dijkstrw/5x5x2/schematic/docs/MUP_U22401/1593657581940577.jpg

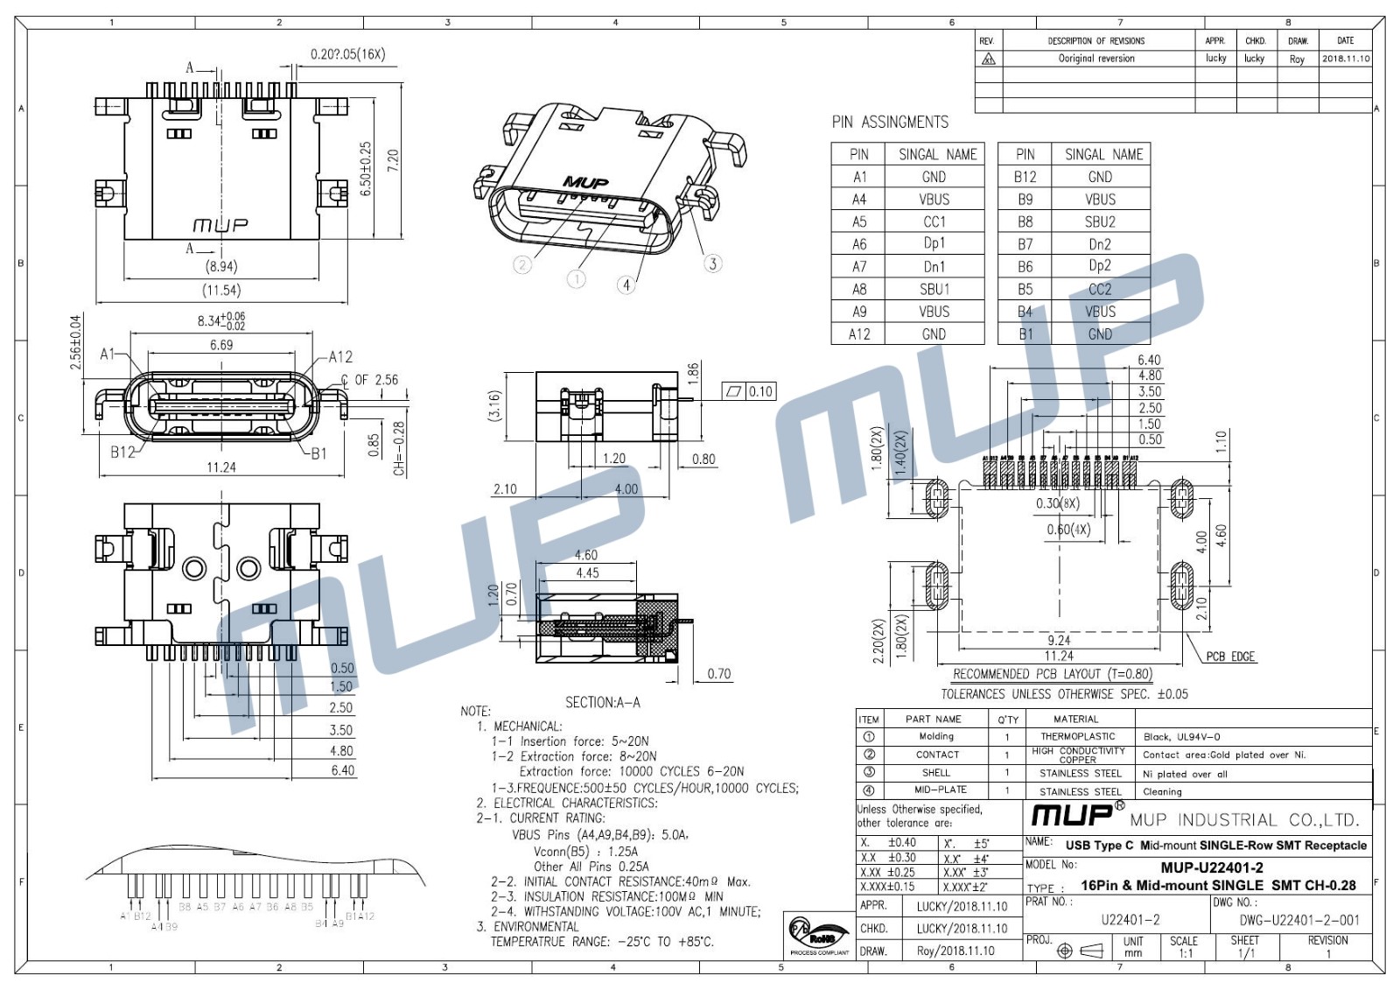
schematic/docs/MUP_U22401/1593657581940577.jpg
