dijkstrw/5x5x2/schematic/docs/MUP_U22401/1593657582415781.jpg

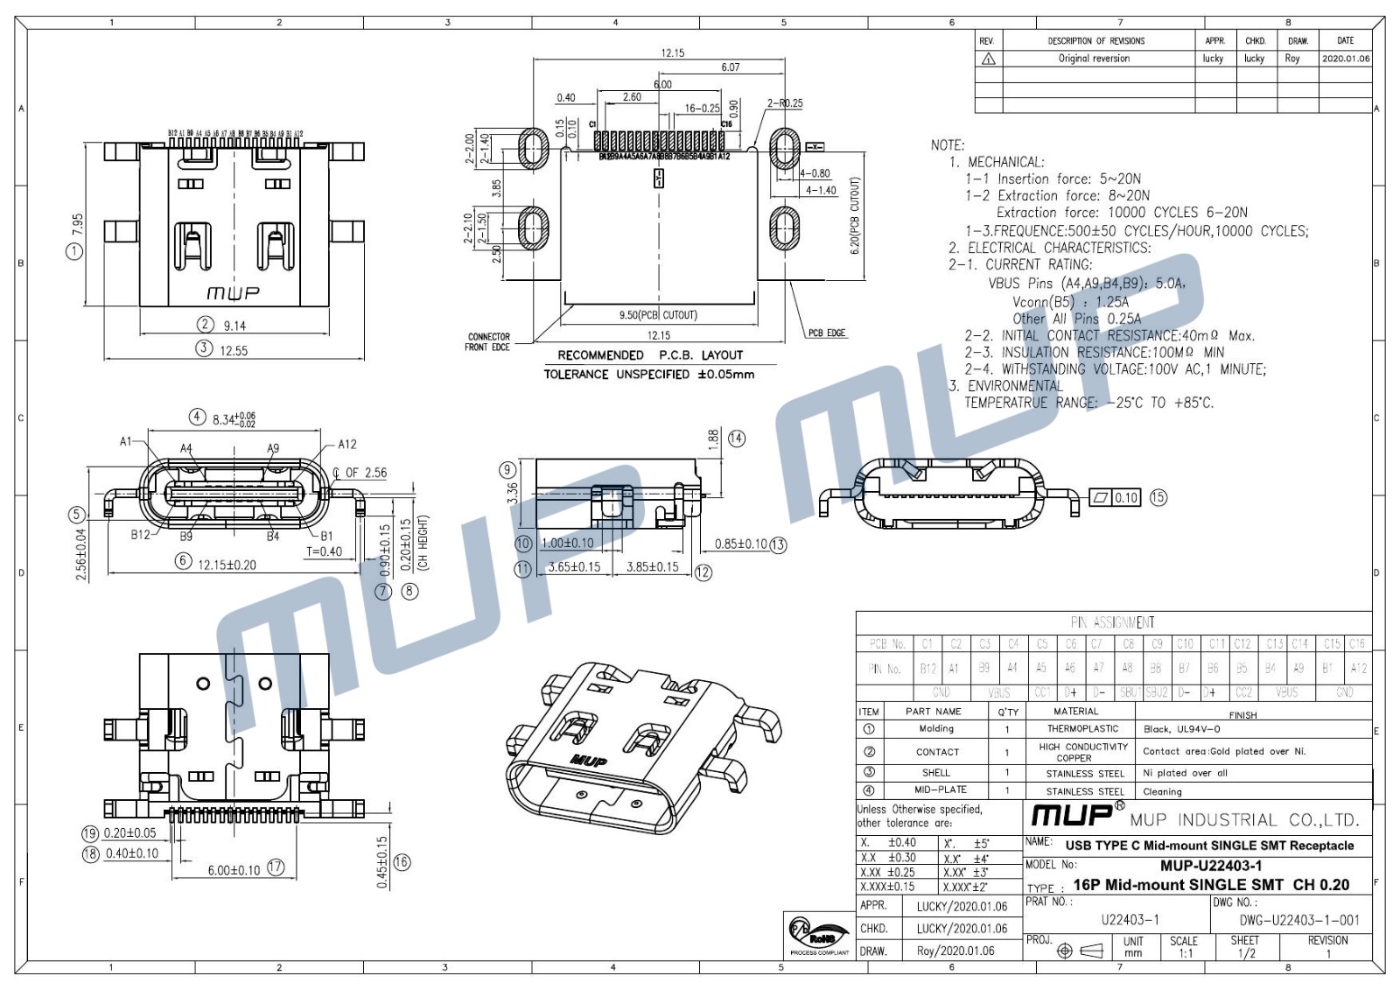
schematic/docs/MUP_U22401/1593657582415781.jpg
