dijkstrw/5x5x2/schematic/docs/MUP_U22401/1593657582979578.jpg

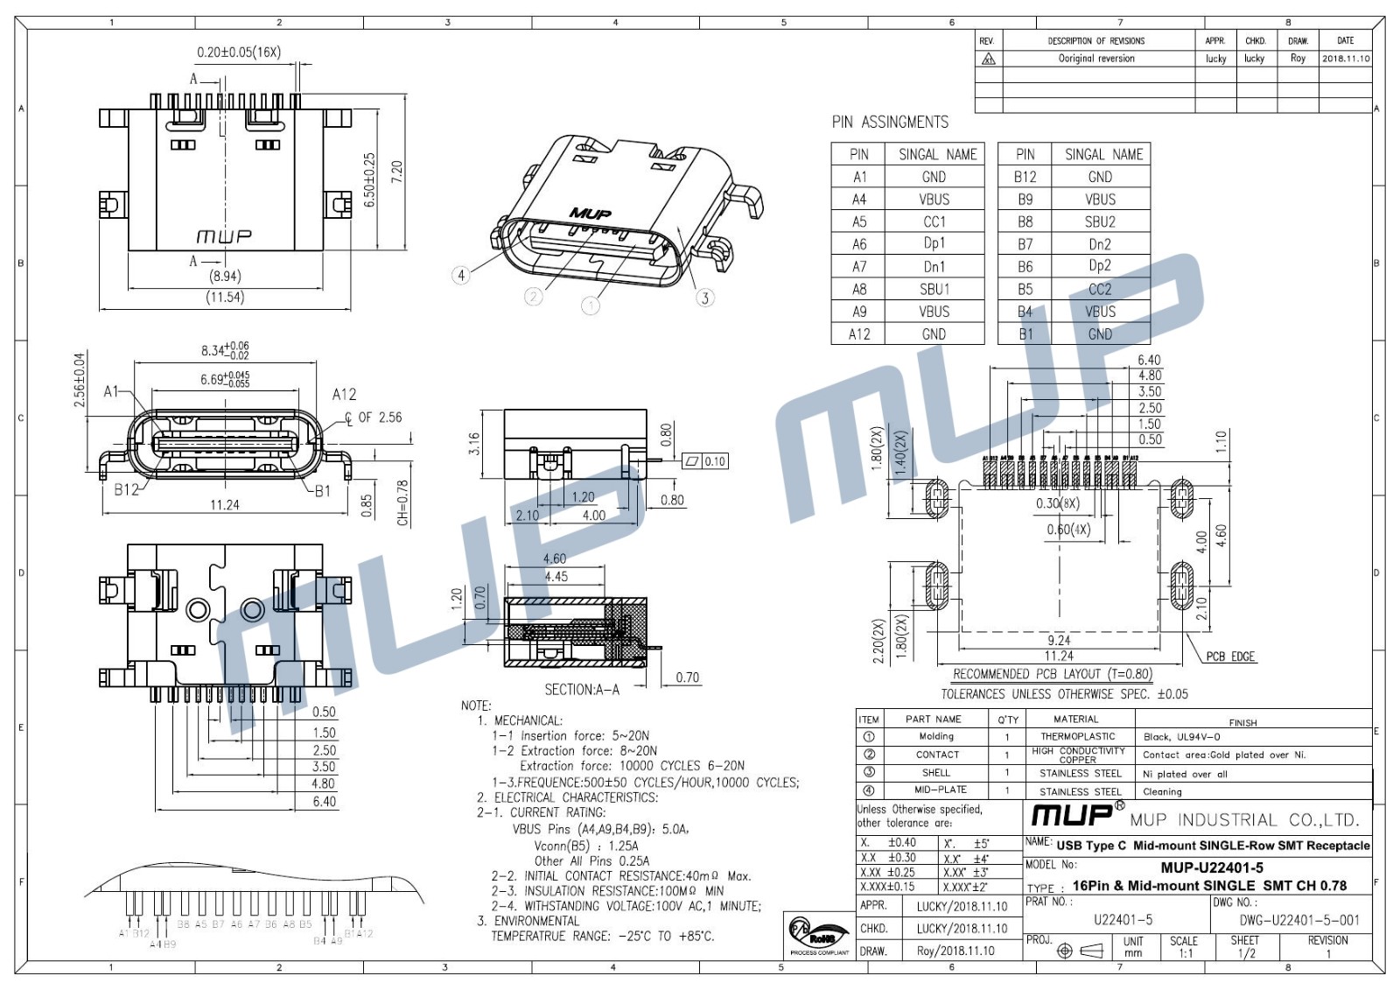
schematic/docs/MUP_U22401/1593657582979578.jpg
