dijkstrw/5x5x2/enclosure/third_plate.scad

include <dimension.scad>;
include <plate.scad>;

if (PROJECTION) {
  projection()
    third_plate();
 } else {
  third_plate();
 }
