dijkstrw/5x5x2/enclosure/top_plate.scad

include <plate.scad>;

if (PROJECTION) {
  projection(cut=true)
    top_plate();
 } else {
  top_plate();
 }
