dijkstrw/5x5x2/light.c

/*
 * Copyright (c) 2023 by Willem Dijkstra <wpd@xs4all.nl>.
 * All rights reserved.
 *
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
 * THIS SOFTWARE IS PROVIDED BY THE COPYRIGHT HOLDERS AND CONTRIBUTORS "AS IS"
 * AND ANY EXPRESS OR IMPLIED WARRANTIES, INCLUDING, BUT NOT LIMITED TO, THE
 * IMPLIED WARRANTIES OF MERCHANTABILITY AND FITNESS FOR A PARTICULAR PURPOSE
 * ARE DISCLAIMED. IN NO EVENT SHALL THE AUTHOR BE LIABLE FOR ANY DIRECT,
 * INDIRECT, INCIDENTAL, SPECIAL, EXEMPLARY, OR CONSEQUENTIAL DAMAGES
 * (INCLUDING, BUT NOT LIMITED TO, PROCUREMENT OF SUBSTITUTE GOODS OR SERVICES;
 * LOSS OF USE, DATA, OR PROFITS; OR BUSINESS INTERRUPTION) HOWEVER CAUSED AND
 * ON ANY THEORY OF LIABILITY, WHETHER IN CONTRACT, STRICT LIABILITY, OR TORT
 * (INCLUDING NEGLIGENCE OR OTHERWISE) ARISING IN ANY WAY OUT OF THE USE OF THIS
 * SOFTWARE, EVEN IF ADVISED OF THE POSSIBILITY OF SUCH DAMAGE.
 */

#include <stdint.h>
#include <string.h>

#include "config.h"
#include "elog.h"
#include "layer.h"
#include "light.h"
#include "macro.h"
#include "palette.h"
#include "rgbease.h"
#include "rgbmap.h"

lightmap_t lightmap =
{
    .data[0] = {
        { LIGHT_DESKTOP, LIGHT_DESKTOP, LIGHT_DESKTOP, LIGHT_DESKTOP, LIGHT_MUTE       },
        { LIGHT_DESKTOP, LIGHT_DESKTOP, LIGHT_DESKTOP, LIGHT_DESKTOP, LIGHT_DESKTOP    },
        { LIGHT_VOLUME,  LIGHT_VOLUME,  LIGHT_VOLUME,  LIGHT_VOLUME,  LIGHT_VOLUME     },
        { LIGHT_MACRO,   LIGHT_MACRO,   LIGHT_MACRO,   LIGHT_MACRO,   LIGHT_MACRO      },
        { LIGHT_LAYER,   LIGHT_LAYER,   LIGHT_DESKTOP, LIGHT_DESKTOP, LIGHT_BACKLIGHT  },
    },
    {
        { LIGHT_DESKTOP, LIGHT_DESKTOP, LIGHT_DESKTOP, LIGHT_DESKTOP, LIGHT_MUTE       },
        { LIGHT_DESKTOP, LIGHT_DESKTOP, LIGHT_DESKTOP, LIGHT_DESKTOP, LIGHT_DESKTOP    },
        { LIGHT_VOLUME,  LIGHT_VOLUME,  LIGHT_VOLUME,  LIGHT_VOLUME,  LIGHT_VOLUME     },
        { LIGHT_MACRO,   LIGHT_MACRO,   LIGHT_MACRO,   LIGHT_MACRO,   LIGHT_MACRO      },
        { LIGHT_LAYER,   LIGHT_LAYER,   LIGHT_DESKTOP, LIGHT_DESKTOP, LIGHT_BACKLIGHT  },
    },
    {
        { LIGHT_DESKTOP, LIGHT_DESKTOP, LIGHT_DESKTOP, LIGHT_DESKTOP, LIGHT_MUTE       },
        { LIGHT_DESKTOP, LIGHT_DESKTOP, LIGHT_DESKTOP, LIGHT_DESKTOP, LIGHT_DESKTOP    },
        { LIGHT_VOLUME,  LIGHT_VOLUME,  LIGHT_VOLUME,  LIGHT_VOLUME,  LIGHT_VOLUME     },
        { LIGHT_MACRO,   LIGHT_MACRO,   LIGHT_MACRO,   LIGHT_MACRO,   LIGHT_MACRO      },
        { LIGHT_LAYER,   LIGHT_LAYER,   LIGHT_DESKTOP, LIGHT_DESKTOP, LIGHT_BACKLIGHT  },
    },
};

lightstate_t light_state;

void
light_dump()
{
    uint8_t l, r, c;

    for (l = 0; l < LAYERS_NUM; l++) {
        printfnl("layer %02x", l);
        for (r = 0; r < ROWS_NUM; r++) {
            printf("row %02x: ", r);
            for (c = 0; c < COLS_NUM; c++) {
                printf("%c ", lightmap.data[l][r][c]);
            }
            printf("\n\r");
        }
    }
}

void
light_init()
{
    memset(&light_state, 0, sizeof(light_state));
}

void
light_set(uint8_t l, uint8_t r, uint8_t c, uint8_t v)
{
    if ((l >= LAYERS_NUM) ||
        (r >= ROWS_NUM) ||
        (c >= COLS_NUM)) {
        elog("light position out of bounds");
        return;
    }

    if ((v == LIGHT_BACKLIGHT) ||
        (v == LIGHT_DESKTOP) ||
        (v == LIGHT_LAYER) ||
        (v == LIGHT_MACRO) ||
        (v == LIGHT_MUTE) ||
        (v == LIGHT_VOLUME)) {
        lightmap.data[l][r][c] = v;
    } else {
        elog("light type unknown");
    }
}

void
light_set_desktop(uint8_t ascreen, uint8_t adisplay)
{
    uint8_t s = ascreen % SCREENS_NUM;

    if (ascreen == 0) {
        for (s = 0; s < SCREENS_NUM; s++) {
            light_state.desktop[s] = adisplay;
        }
    } else {
        light_state.desktop[s - 1] = adisplay;
        if (s > light_state.max_screen) {
            light_state.max_screen = s;
        }
    }
    light_apply_state(LIGHT_DESKTOP);
}

void
light_set_layer(uint8_t alayer)
{
    light_apply_state(0);
}

void
light_set_macro(uint8_t amacro)
{
    light_apply_state(LIGHT_MACRO);
}

void
light_set_mic_mute(uint8_t astate)
{
    light_state.mic_mute = astate;
    light_apply_state(LIGHT_MUTE);
}

void
light_set_mute(uint8_t astate)
{
    light_state.mute = astate;
    light_apply_state(LIGHT_MUTE);
}

void
light_set_volume(uint16_t avolume)
{
    light_state.volume = avolume;
    light_apply_state(LIGHT_VOLUME);
}

static hsv_t
_light_rainbow_color(uint8_t num, uint8_t i)
{
    hsv_t color = HSV_RED;
    color.h += (HUE_MAX / num) * i;

    return color;
}

void
light_apply_state(uint8_t only_type)
{
    uint8_t r, c;
    uint8_t id, typ;
    uint8_t screen = 0;
    uint8_t num_backlight = 0, i_backlight = 0;
    hsv_t color;

    for (r = 0; r < ROWS_NUM; r++) {
        for (c = 0; c < COLS_NUM; c++) {
            typ = lightmap.data[layer][r][c];
            if ((typ == LIGHT_BACKLIGHT) || (typ == LIGHT_MACRO)) {
                num_backlight++;
            }
        }
    }

    for (r = 0; r < ROWS_NUM; r++) {
        for (c = 0; c < COLS_NUM; c++) {
            typ = lightmap.data[layer][r][c];
            if (only_type && (typ != only_type)) {
                continue;
            }
            id = key2led(r, c);

            switch (typ) {
            case LIGHT_BACKLIGHT:
                rgbease_set(id, _light_rainbow_color(num_backlight, i_backlight), F_SLOW_RAINBOW, 0 , 0);
                i_backlight++;
                break;

            case LIGHT_DESKTOP:
                color = palette_get(COLOR_DESKTOP + light_state.desktop[screen]);
                rgbease_set(id, color, F_COLOR_HOLD, 0, 0);
                screen = (screen + 1) % light_state.max_screen;
                break;

            case LIGHT_LAYER:
                color = palette_get(COLOR_LAYER + layer);
                rgbease_set(id, color, F_COLOR_HOLD, 0, 0);
                break;

            case LIGHT_MACRO:
                if (macro_active) {
                    color = palette_get(COLOR_MACRO);
                    rgbease_set(id, color, F_COLOR_FLASHING, 0, 0);
                } else {
                    rgbease_set(id, _light_rainbow_color(num_backlight, i_backlight), F_SLOW_RAINBOW, 0 , 0);
                    i_backlight++;
                }
                break;

            case LIGHT_MUTE:
            case LIGHT_MIC_MUTE:
               if (light_state.mic_mute) {
                   if (light_state.mute) {
                       color = hsv_red;
                   } else {
                       color = hsv_magenta;
                   }
               } else {
                   if (light_state.mute) {
                       color = hsv_yellow;
                   } else {
                       color = hsv_green;
                   }
               }
               rgbease_set(id, color, F_COLOR_HOLD, STEP_FAST, 0);
               break;

            case LIGHT_VOLUME:
                color = hsv_yellow;
                color.h = LIGHT_VOLUME_TO_HUE(light_state.volume);
                rgbease_set(id, color, F_COLOR_HOLD, STEP_FAST, 0);
                break;
            }
        }
    }
}
