dijkstrw/5x5x2/light.h

/*
 * Copyright (c) 2023 by Willem Dijkstra <wpd@xs4all.nl>.
 * All rights reserved.
 *
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
 * THIS SOFTWARE IS PROVIDED BY THE COPYRIGHT HOLDERS AND CONTRIBUTORS "AS IS"
 * AND ANY EXPRESS OR IMPLIED WARRANTIES, INCLUDING, BUT NOT LIMITED TO, THE
 * IMPLIED WARRANTIES OF MERCHANTABILITY AND FITNESS FOR A PARTICULAR PURPOSE
 * ARE DISCLAIMED. IN NO EVENT SHALL THE AUTHOR BE LIABLE FOR ANY DIRECT,
 * INDIRECT, INCIDENTAL, SPECIAL, EXEMPLARY, OR CONSEQUENTIAL DAMAGES
 * (INCLUDING, BUT NOT LIMITED TO, PROCUREMENT OF SUBSTITUTE GOODS OR SERVICES;
 * LOSS OF USE, DATA, OR PROFITS; OR BUSINESS INTERRUPTION) HOWEVER CAUSED AND
 * ON ANY THEORY OF LIABILITY, WHETHER IN CONTRACT, STRICT LIABILITY, OR TORT
 * (INCLUDING NEGLIGENCE OR OTHERWISE) ARISING IN ANY WAY OUT OF THE USE OF THIS
 * SOFTWARE, EVEN IF ADVISED OF THE POSSIBILITY OF SUCH DAMAGE.
 */

#ifndef _LIGHT_H
#define _LIGHT_H

#include <stdint.h>

#include "config.h"
#include "flash.h"

/* The keyboard has 5x5 + 8 leds and can show a variety of statusses.
 *
 * These "system events" can reach us from either:
 * - a key (up/down) event
 * - a system event signalled to us via serial
 *
 * Classes of "system events" we want to display are:
 *
 * - desktop number changed -- display the current desktop number on a
 *   key or keygroup using a color from the palette.
 *
 * - sound mute enabled/disabled -- could be done by using red on the
 *   lower lights to indicate that sound is muted.
 *
 * - microphone mute enabled/disabled -- could be done by using purple
 *   on the lower lights to indicate that the microphone is muted.
 *
 * - layer number changed -- display the current layer number on a key
 *   or keygroup using a color from the palette.
 *
 * - autokey running -- autokey will wreak havoc on any other
 *   keypresses, so clearly displaying that the keyboard is spamming
 *   away is crucial.
 *
 * - automouse running -- automouse will still allow keypresses, but
 *   can be in the way of normal mousework, so this too must be
 *   clearly visible.
 *
 * - vumeter -- color information coming from serial that maps to
 *   audio played by the main system.
 *
 * Some of these events can happen on the host, so we need to be able
 * to communicate these via serial:
 *
 * D T SS DD
 * | |  | |
 * | |  | ╰ Desktop 01-10
 * | |  ╰-- Screen 00 = all, 01-04 a specific one
 * | ╰----- 'D' for desktop
 * ╰------- 'D' fixed, to indicate 'D'isplay event / 'D'esktop event
 *
 * D T MM
 * | |  |
 * | |  ╰-- Mute status 00 = not muted, 01 = muted
 * | ╰----- 'M' for sound output, 'R' for mic input
 * ╰------- 'D' fixed, to indicate 'D'isplay event / 'D'esktop event
 *
 * D T VVVV
 * | |  |
 * | |  ╰-- Volume 0000 - ffff
 * | ╰----- 'V' for volume
 * ╰------- 'D' fixed, to indicate 'D'isplay event / 'D'esktop event
 *
 */

enum {
    LIGHT_ALL             = 0,
    LIGHT_AUTOMOUSE       = 'A',
    LIGHT_BACKLIGHT       = 'B',
    LIGHT_DESKTOP         = 'D',
    LIGHT_LAYER           = 'L',
    LIGHT_MACRO           = 'm',
    LIGHT_MIC_MUTE        = 'R',
    LIGHT_MUTE            = 'M',
    LIGHT_VOLUME          = 'V',
};

#define _LIGHTMAP_SIZE        (LAYERS_NUM * ROWS_NUM * COLS_NUM)
#define _LIGHTMAP_FLASH_SIZE  FLASH_ALIGNED_SIZE(_LIGHTMAP_SIZE)

typedef struct {
    uint8_t data[LAYERS_NUM][ROWS_NUM][COLS_NUM];
    uint8_t padding[_LIGHTMAP_FLASH_SIZE - _LIGHTMAP_SIZE];
} __attribute__ ((packed)) lightmap_t;

typedef struct {
    uint8_t desktop[SCREENS_NUM];
    uint8_t max_screen;
    uint8_t mic_mute;
    uint8_t mute;
    uint16_t volume;
} lightstate_t;

/*
 * The hsv color range ranges from red at 0° to red at 360°. To
 * display volume levels we want to use yellow at 60° ranging to red
 * at 360°.
 *
 * Looking at color inputs we need to supply a hsv_t, where the hue
 * component is expressed internally as 0 to 0x600, with 0x600
 * representing 360°.
 *
 * yellow at 60° is 0x100 and we can range to 0x0600.
 * map to volume    0x0                       0xffff.
 */

#define _VOL_RANGE_DIV         ((0xFFFF / 0x500) + 1)
#define LIGHT_VOLUME_TO_HUE(v) (HUE_SEXTANT + (v / _VOL_RANGE_DIV))

extern lightmap_t lightmap;

void light_dump();
void light_init(void);
void light_apply_state(uint8_t only_type);
void light_set(uint8_t l, uint8_t r, uint8_t c, uint8_t v);
void light_set_desktop(uint8_t screen, uint8_t display);
void light_set_layer(uint8_t layer);
void light_set_macro(uint8_t amacro);
void light_set_mic_mute(uint8_t state);
void light_set_mute(uint8_t state);
void light_set_volume(uint16_t volume);

#endif /* _LIGHT_H */
